vigibot/vigicad/images/Minus assembly/Final assembly-7.png

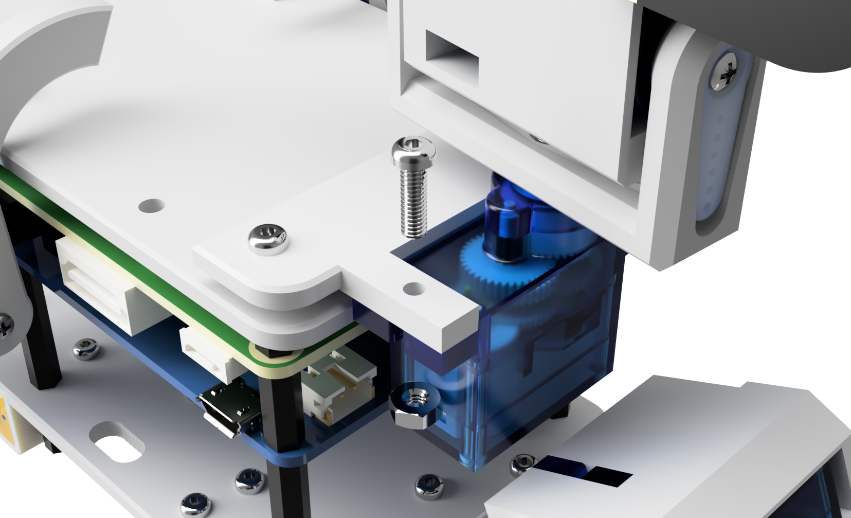
images/Minus assembly/Final assembly-7.png
