vigibot/vigicad/images/Minus render-1.png

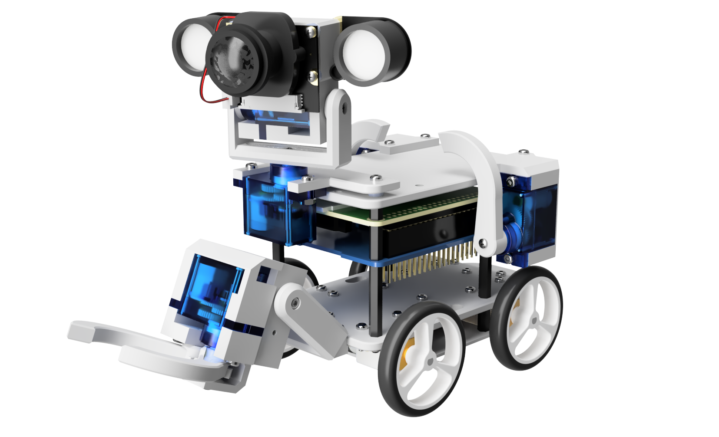
images/Minus render-1.png
