vigibot/vigicad/images/Minus render-2.png

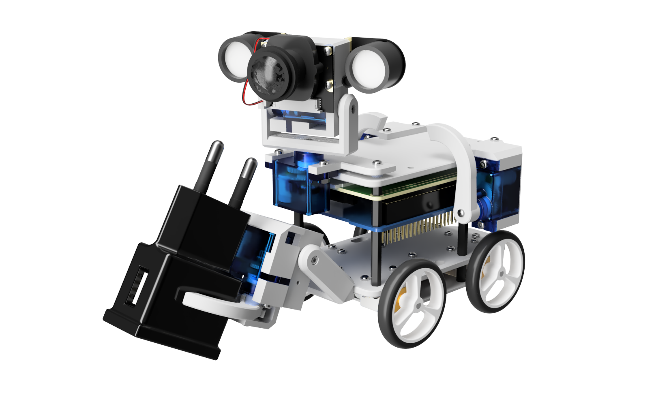
images/Minus render-2.png
