vigibot/vigicad/Minus 2S/Images/Minus 2s.jpg

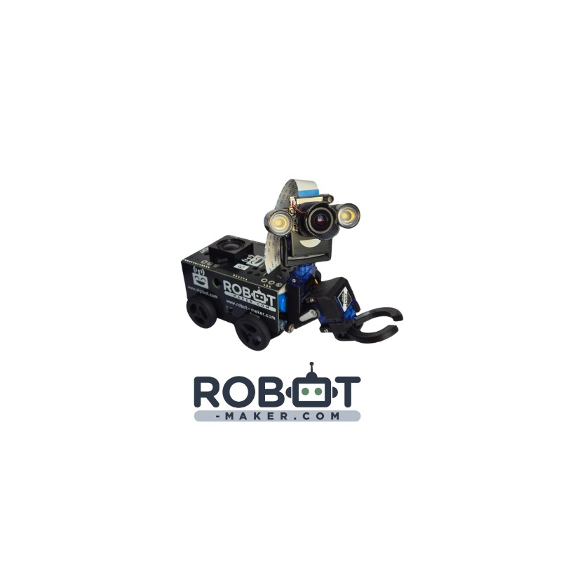
Minus 2S/Images/Minus 2s.jpg
