vigibot/vigicad/Minus 2S/3d Printed Parts/Body/Battery holder.step

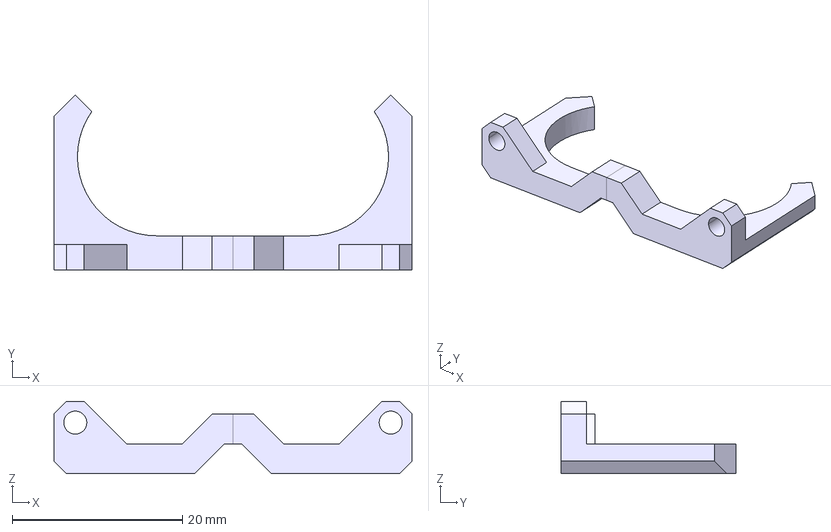
[picture p20: CAD file, 2026-06-20]
Minus 2S/3d Printed Parts/Body/Battery holder.step
42.0 x 20.5 x 8.50 mm
