vigibot/vigicad/Minus 2S/3d Printed Parts/Gripper/Gripper left finger.step

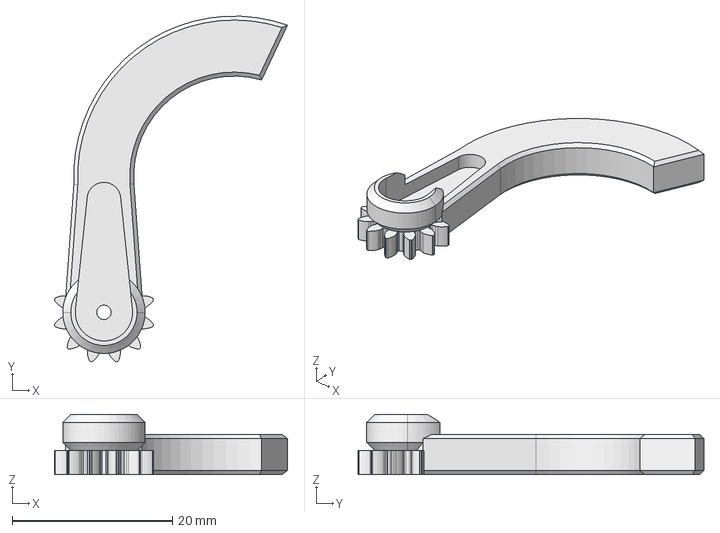
[picture p21: CAD file, 2026-06-20]
Minus 2S/3d Printed Parts/Gripper/Gripper left finger.step
29.1 x 43.1 x 7.50 mm
