vigibot/vigicad/Minus 2S/Pcb Boards/Head Led Pcb.step

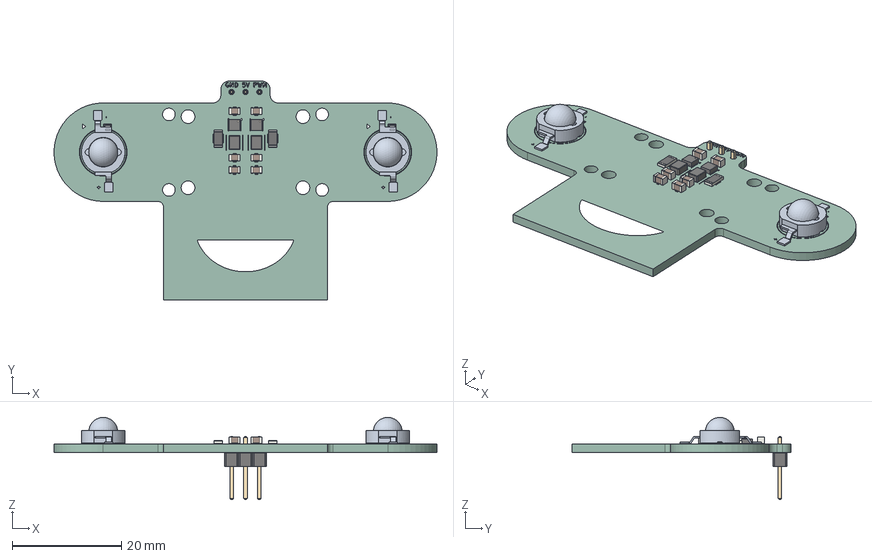
[picture p22: CAD file, 2026-06-20]
Minus 2S/Pcb Boards/Head Led Pcb.step
70.0 x 40.0 x 15.0 mm
C_0805_2012Metric x 6
L_Changjiang_FTC252012S x 2
R_1206_3216Metric x 2
Power Led x 2
WSON-6-1EP_2x2mm_P0.65mm_EP1x1.6mm x 2
PinHeader_1x03_P2.54mm_Vertical
Addon_head_silkscreen x 2
Addon_head_PCB
