vigibot/vigicad/3mf/rear_protection_long.3mf

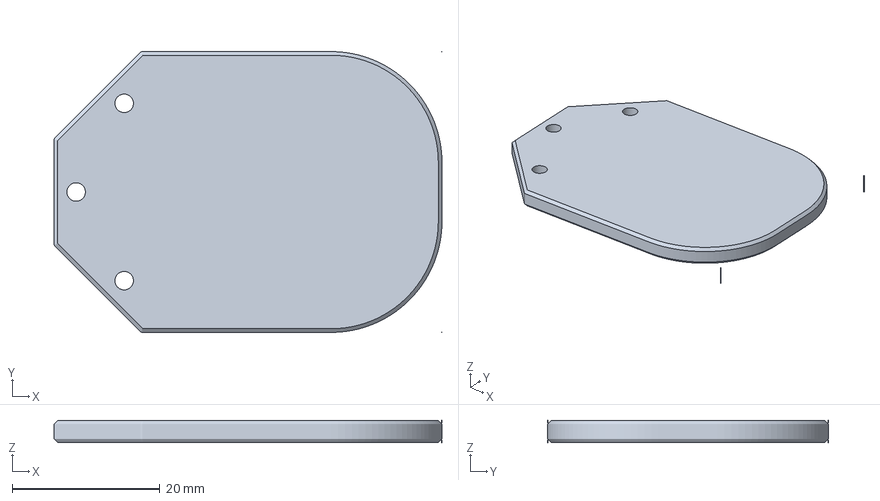
[picture p23: CAD file, 2019-10-13]
3mf/rear_protection_long.3mf
52.5 x 38.0 x 3.00 mm
