vigibot/vigicad/3mf/plate_middle_big_wheels.3mf

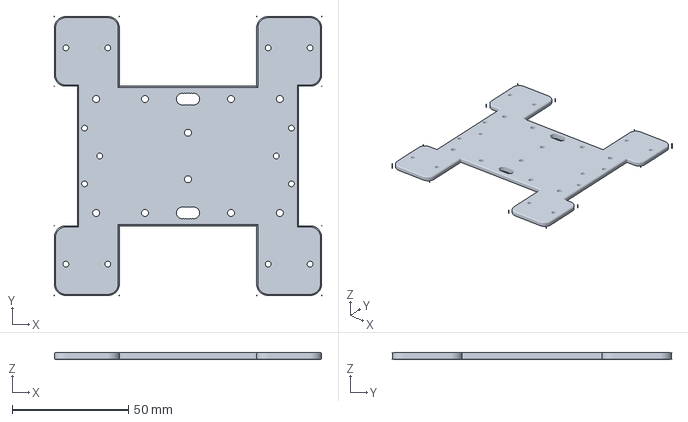
[picture p24: CAD file, 2019-10-09]
3mf/plate_middle_big_wheels.3mf
115.0 x 120.0 x 3.00 mm
