vigibot/vigicad/stl/UDroit35mm.stl

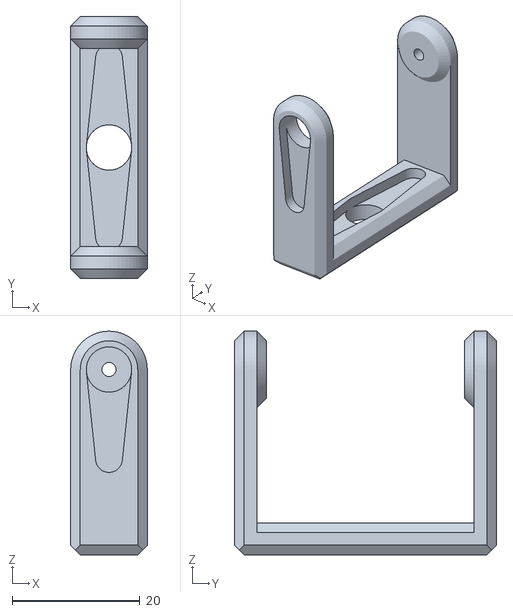
[picture p25: CAD file, 2019-06-25]
stl/UDroit35mm.stl
12.0 x 41.0 x 35.0
