vigibot/vigicad/3mf/head_pan_servo_bracket.3mf

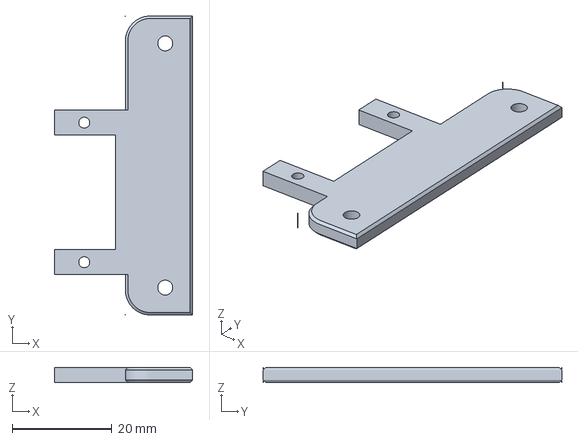
[picture p26: CAD file, 2019-09-12]
3mf/head_pan_servo_bracket.3mf
27.8 x 60.0 x 3.00 mm
