vigibot/vigicad/stl/UDroit30mm.stl

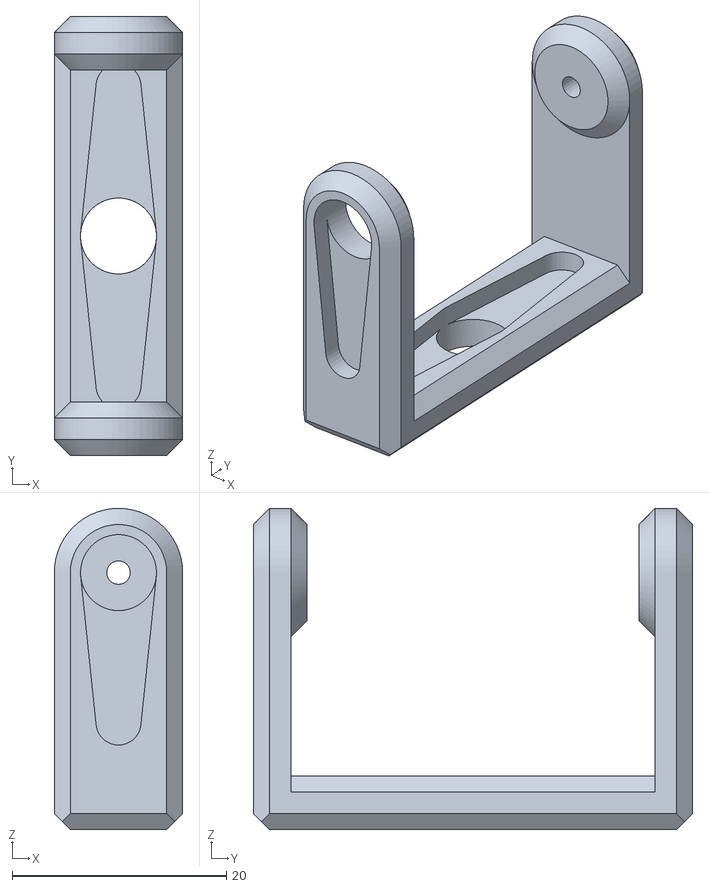
[picture p27: CAD file, 2019-06-25]
stl/UDroit30mm.stl
12.0 x 41.0 x 30.0
