vigibot/vigicad/3mf/generic_servo_bracket.3mf

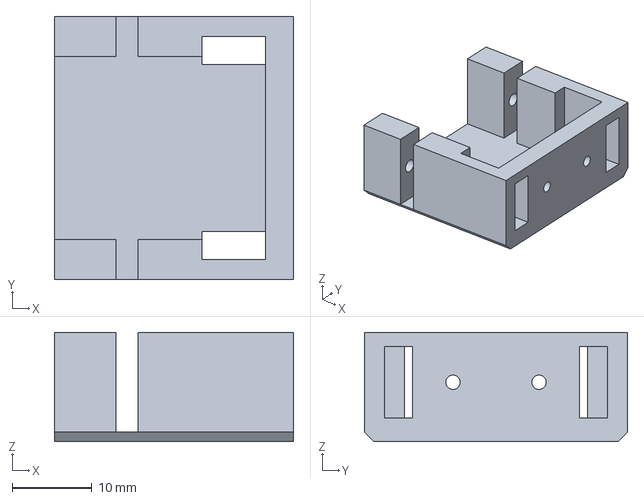
[picture p28: CAD file, 2019-09-08]
3mf/generic_servo_bracket.3mf
30.0 x 33.0 x 13.7 mm
