vigibot/vigicad/stl/UDroit28mm.stl

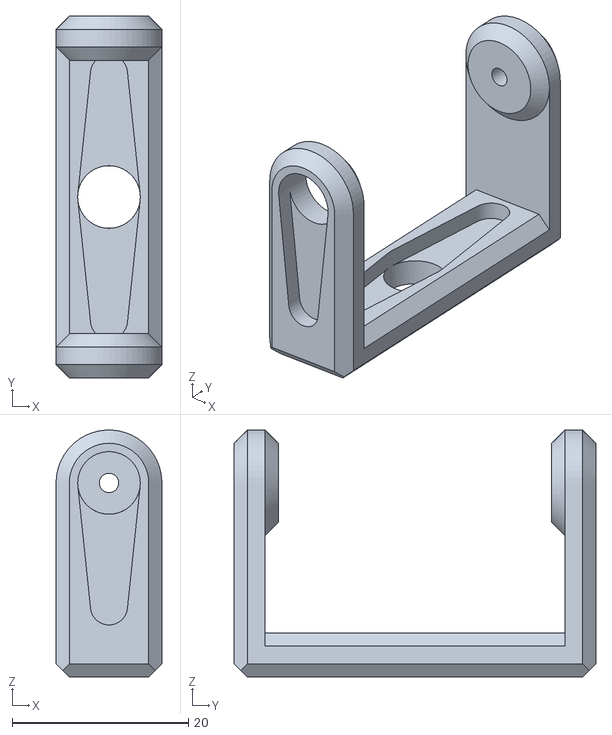
[picture p29: CAD file, 2019-06-25]
stl/UDroit28mm.stl
12.0 x 41.0 x 28.0
