vigibot/vigicad/3mf/usb_bracket.3mf

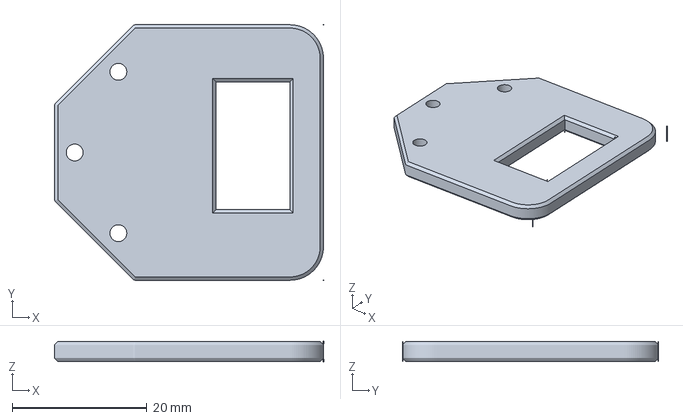
[picture p30: CAD file, 2019-09-07]
3mf/usb_bracket.3mf
40.0 x 38.0 x 3.00 mm
