vigibot/vigicad/3mf/get_up_servo_bracket_b.3mf

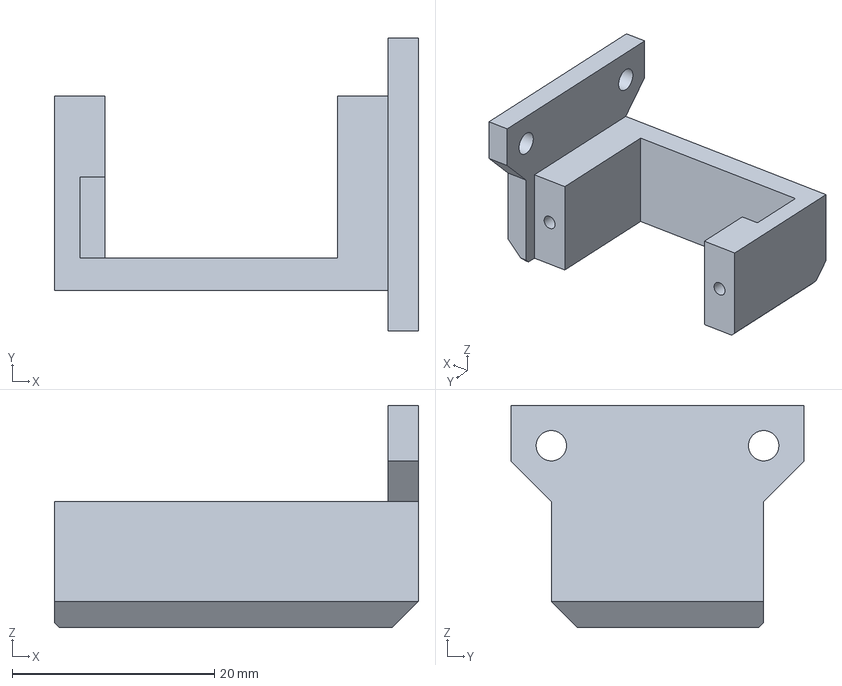
[picture p32: CAD file, 2019-09-06]
3mf/get_up_servo_bracket_b.3mf
36.0 x 29.0 x 22.0 mm
