vigibot/vigicad/3mf/rear_protection.3mf

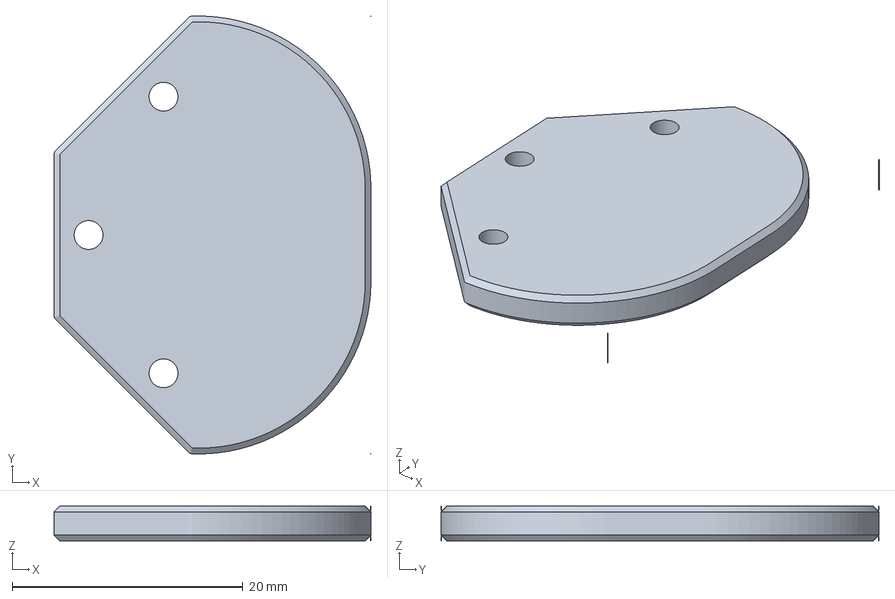
[picture p33: CAD file, 2019-09-06]
3mf/rear_protection.3mf
27.5 x 38.0 x 3.00 mm
