vigibot/vigicad/3mf/clamp_finger_b.3mf

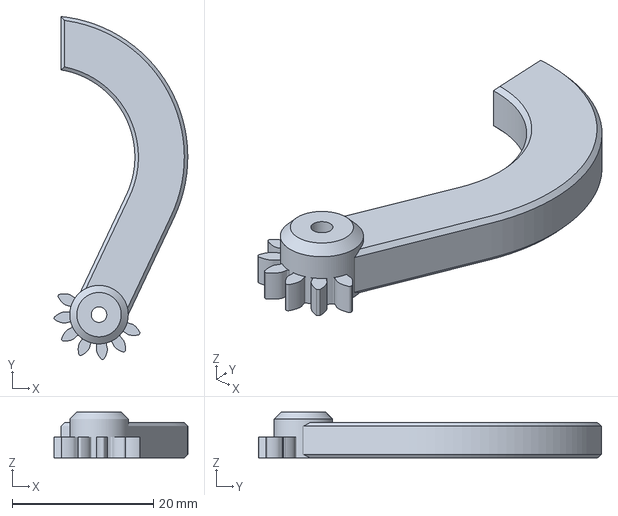
[picture p34: CAD file, 2019-09-06]
3mf/clamp_finger_b.3mf
18.9 x 48.6 x 6.50 mm
