vigibot/vigicad/3mf/plate_middle.3mf

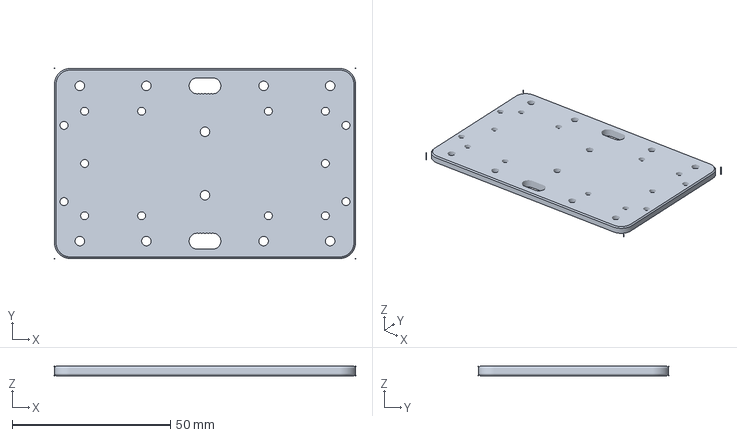
[picture p35: CAD file, 2019-09-06]
3mf/plate_middle.3mf
95.0 x 60.0 x 3.00 mm
