vigibot/vigicad/3mf/servo_finger_a.3mf

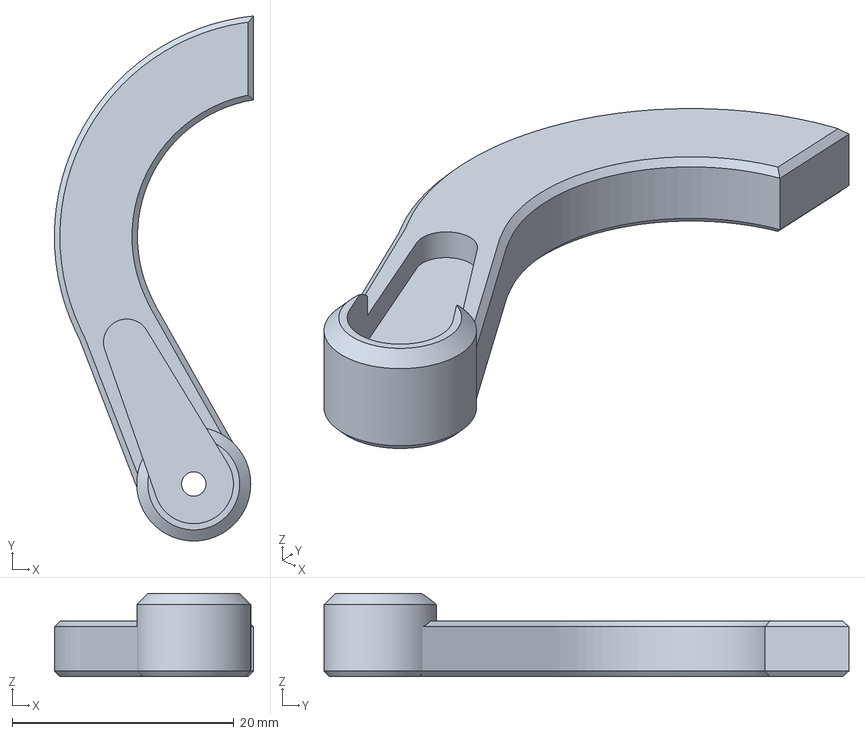
[picture p36: CAD file, 2019-09-06]
3mf/servo_finger_a.3mf
18.0 x 47.3 x 7.50 mm
