vigibot/vigicad/3mf/clamp_u_bracket.3mf

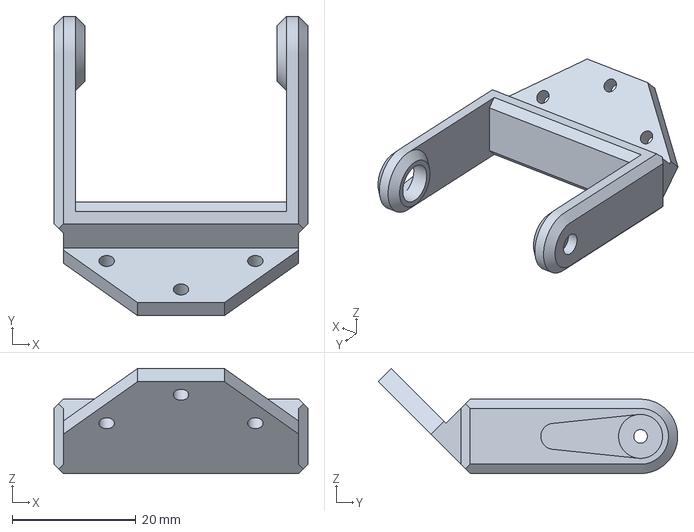
[picture p37: CAD file, 2019-09-06]
3mf/clamp_u_bracket.3mf
41.0 x 48.3 x 17.0 mm
