vigibot/vigicad/3mf/clamp_finger_a.3mf

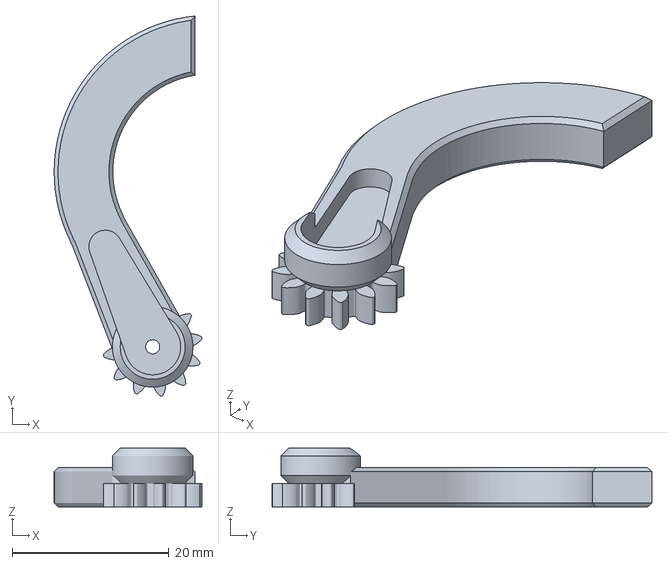
[picture p38: CAD file, 2019-09-06]
3mf/clamp_finger_a.3mf
18.9 x 48.5 x 7.50 mm
