vigibot/vigicad/3mf/plate_top_fan.3mf

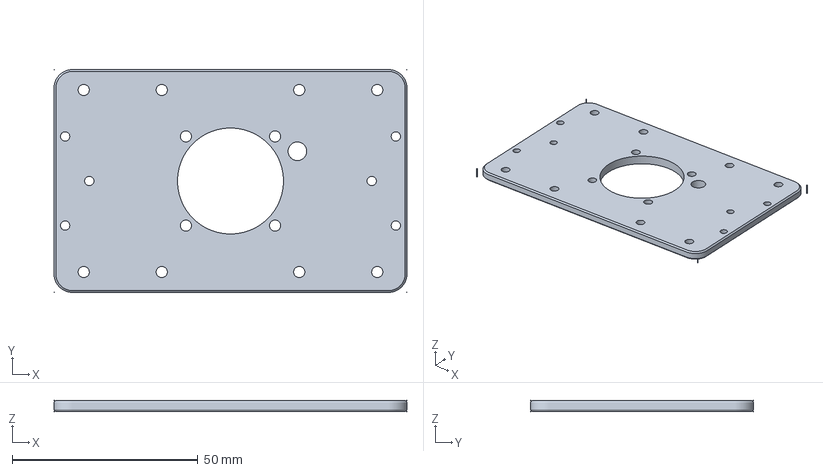
[picture p39: CAD file, 2019-09-06]
3mf/plate_top_fan.3mf
95.0 x 60.0 x 3.00 mm
