vigibot/vigicad/3mf/head_servo_camera_bracket_smile.3mf

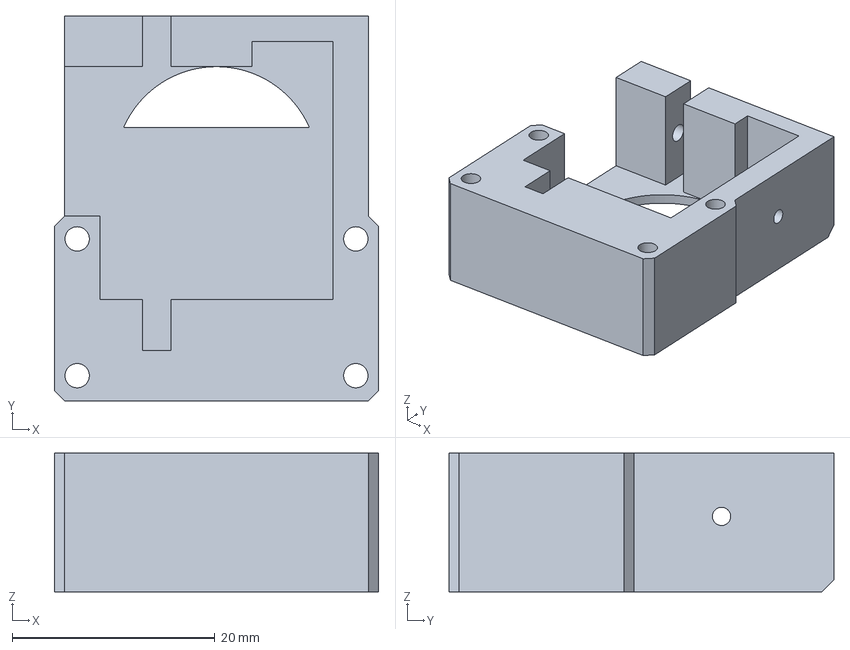
[picture p40: CAD file, 2019-09-06]
3mf/head_servo_camera_bracket_smile.3mf
32.0 x 38.0 x 13.7 mm
