vigibot/vigicad/3mf/photoresistor_cap.3mf

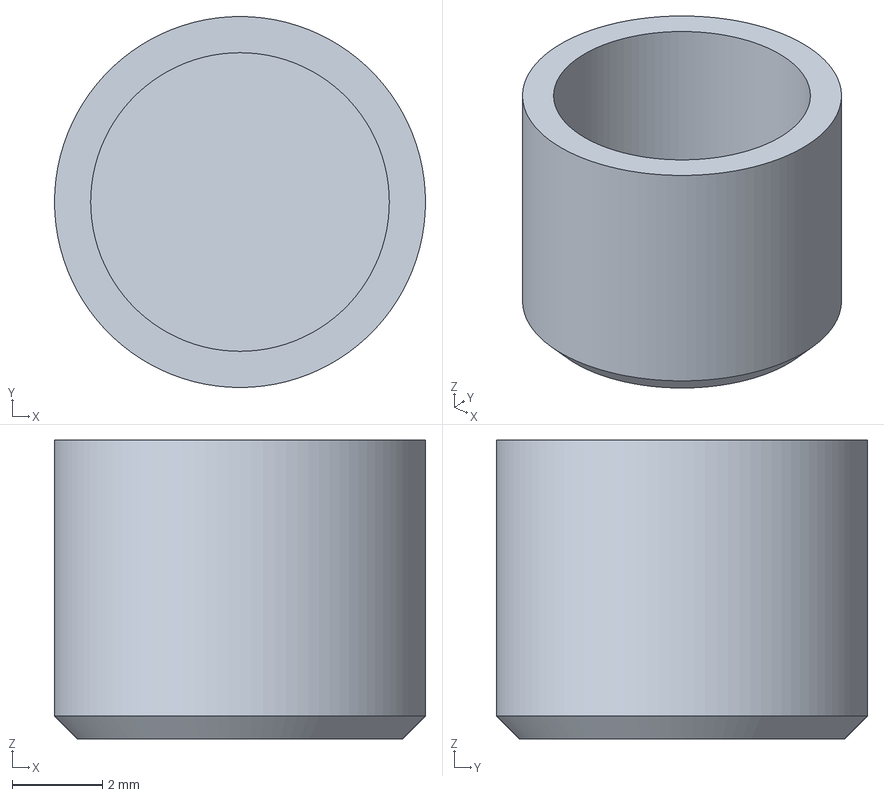
[picture p41: CAD file, 2019-09-06]
3mf/photoresistor_cap.3mf
8.20 x 8.20 x 6.60 mm
