vigibot/vigicad/3mf/plate_bottom.3mf

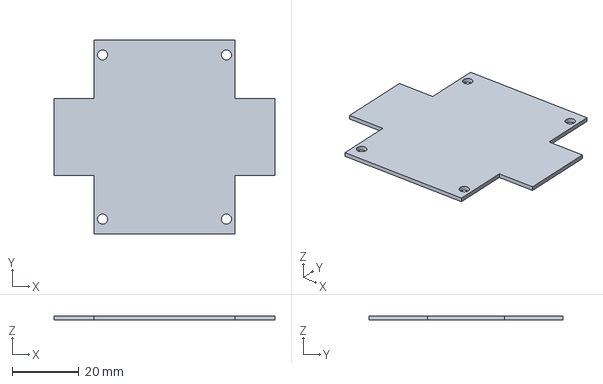
[picture p42: CAD file, 2019-09-06]
3mf/plate_bottom.3mf
66.0 x 58.0 x 1.20 mm
