vigibot/vigicad/images/Minus assembly/Camera assembly-1.png

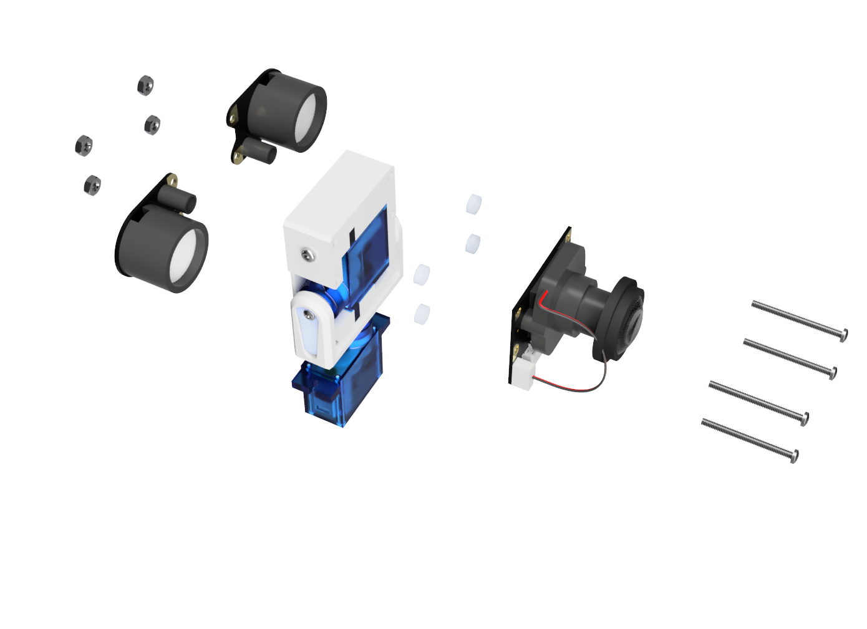
images/Minus assembly/Camera assembly-1.png
