vigibot/vigicad/images/Minus assembly/Camera assembly-2.png

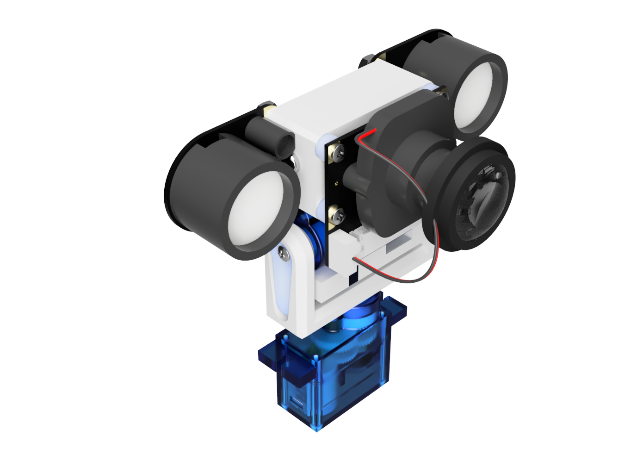
images/Minus assembly/Camera assembly-2.png
