vigibot/vigicad/images/Minus assembly/Final assembly-1.png

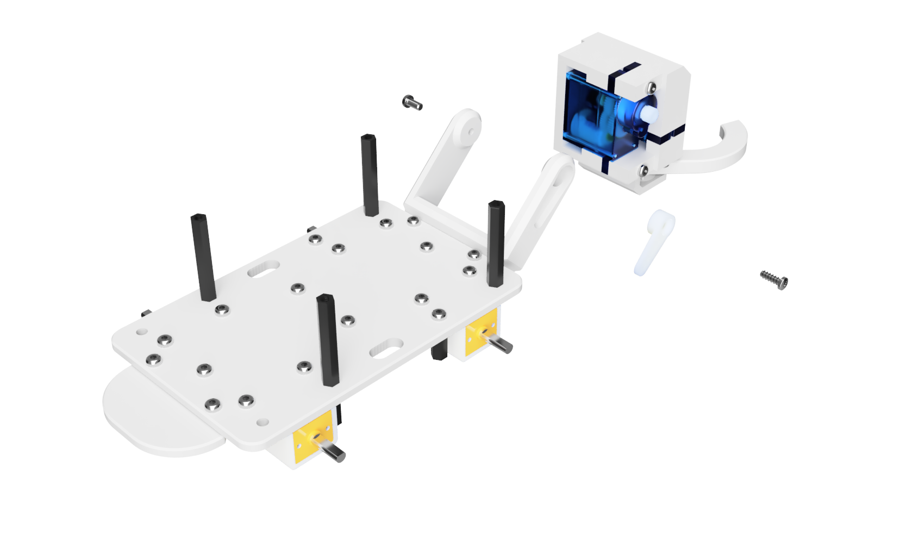
images/Minus assembly/Final assembly-1.png
