vigibot/vigicad/images/Minus assembly/Final assembly-3.png

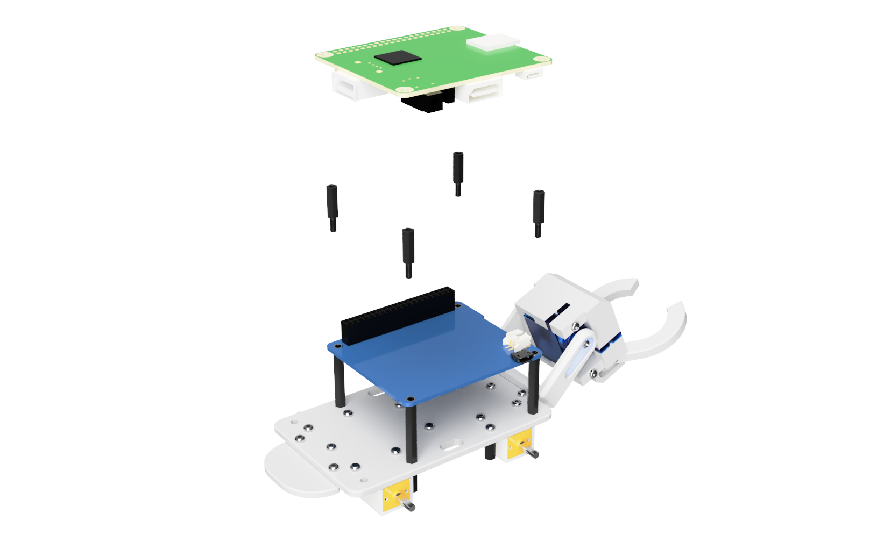
images/Minus assembly/Final assembly-3.png
