vigibot/vigicad/images/Minus assembly/Final assembly-4.png

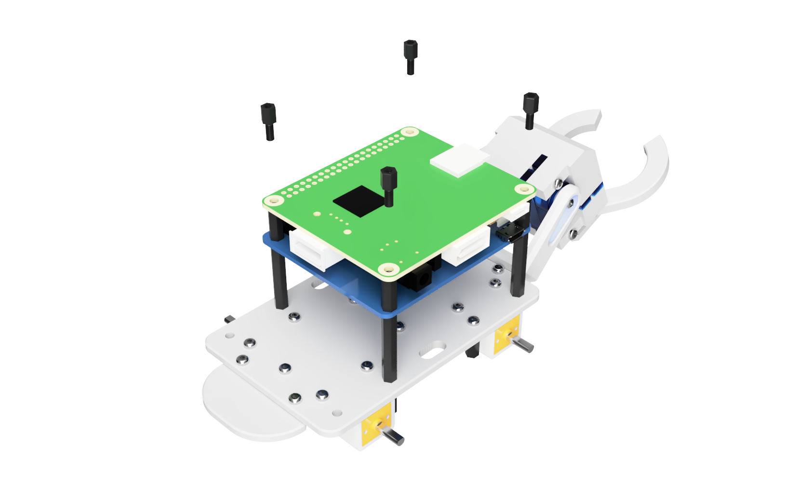
images/Minus assembly/Final assembly-4.png
