vigibot/vigicad/images/Minus assembly/Final assembly-5.png

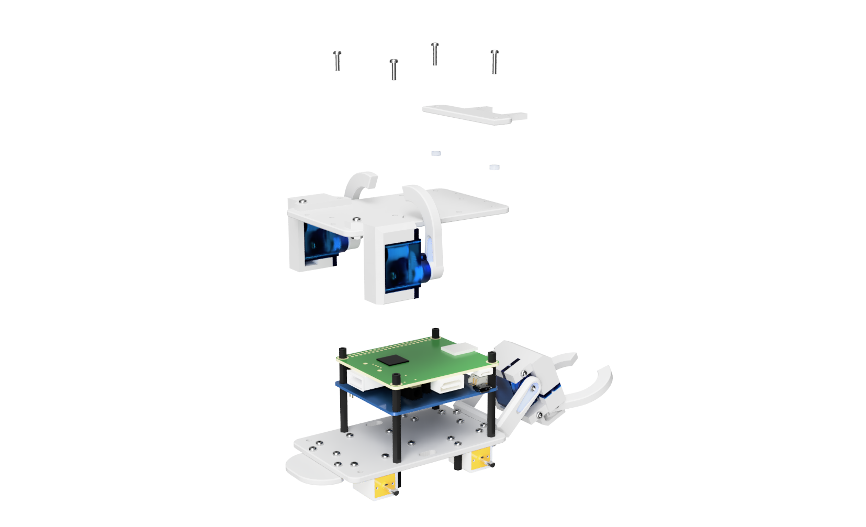
images/Minus assembly/Final assembly-5.png
