vigibot/vigicad/images/Minus assembly/Final assembly-6.png

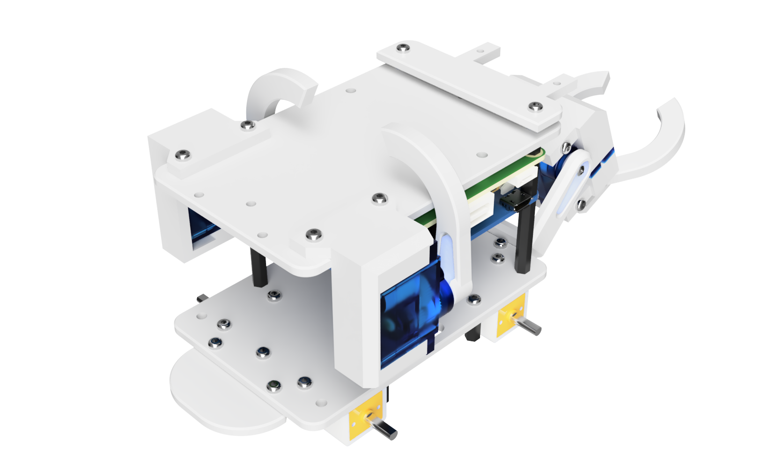
images/Minus assembly/Final assembly-6.png
