vigibot/vigicad/images/Minus assembly/Final assembly-9.png

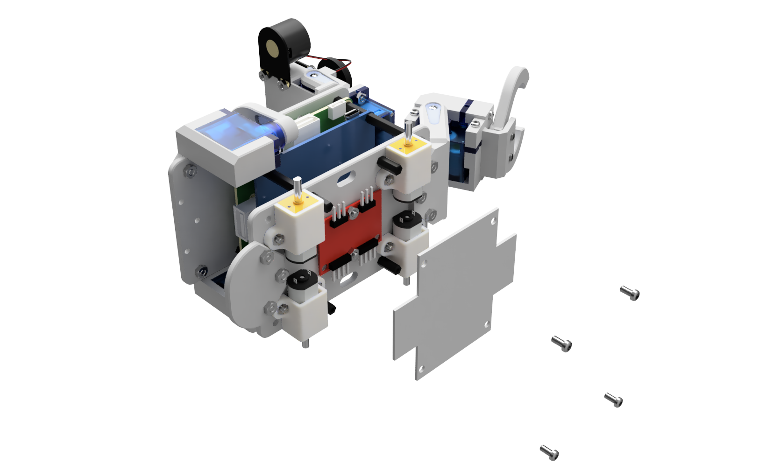
images/Minus assembly/Final assembly-9.png
