vigibot/vigicad/images/Minus assembly/Gripper assembly-1.png

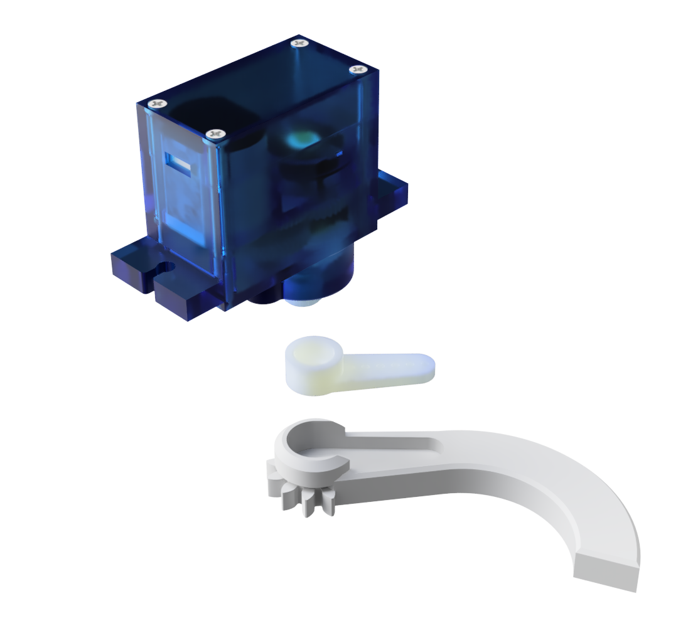
images/Minus assembly/Gripper assembly-1.png
