vigibot/vigicad/images/Minus assembly/Gripper assembly-2.png

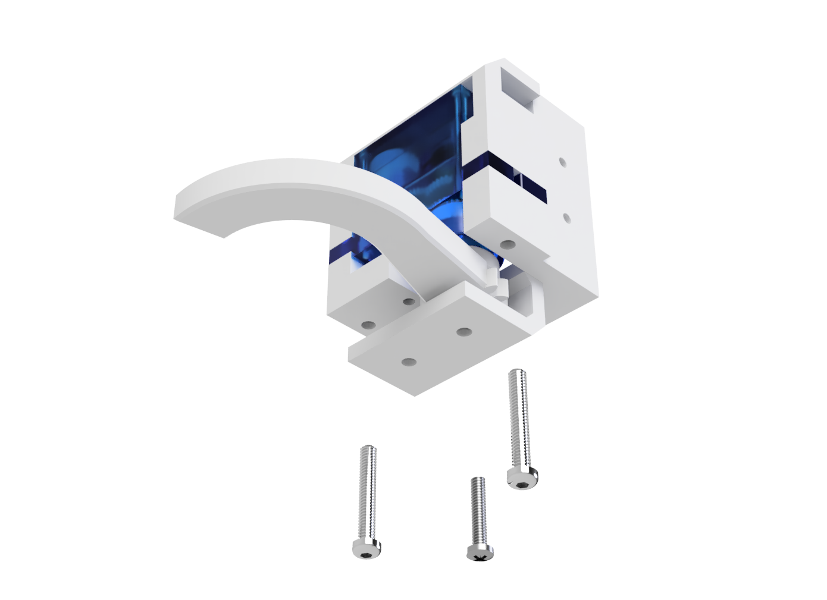
images/Minus assembly/Gripper assembly-2.png
