vigibot/vigicad/images/Minus assembly/Gripper assembly-3.png

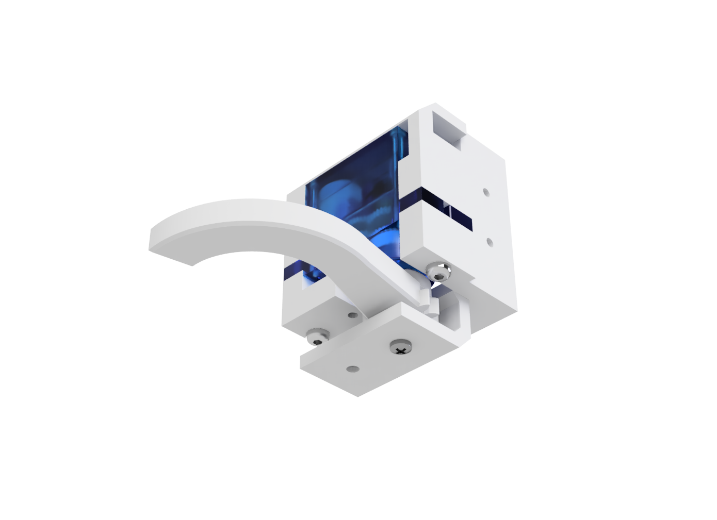
images/Minus assembly/Gripper assembly-3.png
