vigibot/vigicad/images/Minus assembly/Gripper assembly-4.png

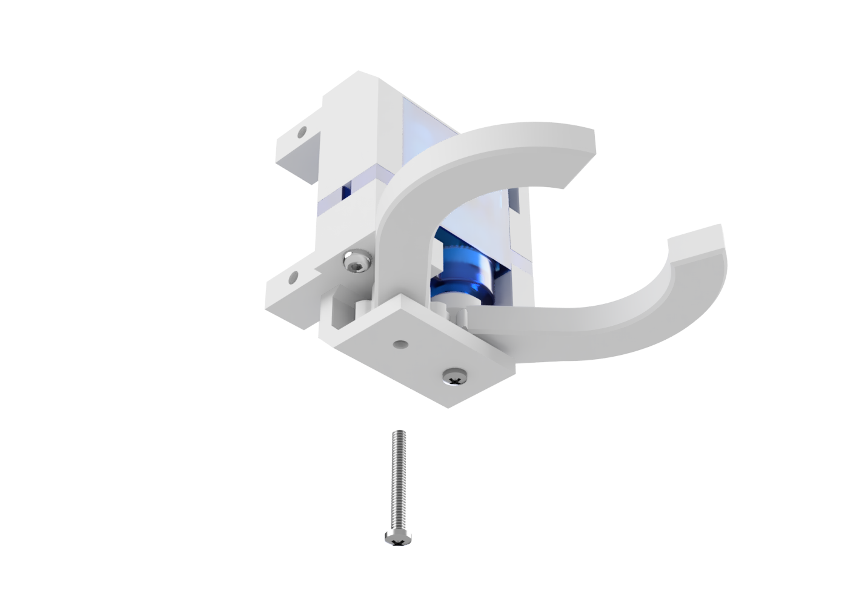
images/Minus assembly/Gripper assembly-4.png
