vigibot/vigicad/images/Minus assembly/Gripper assembly-6.png

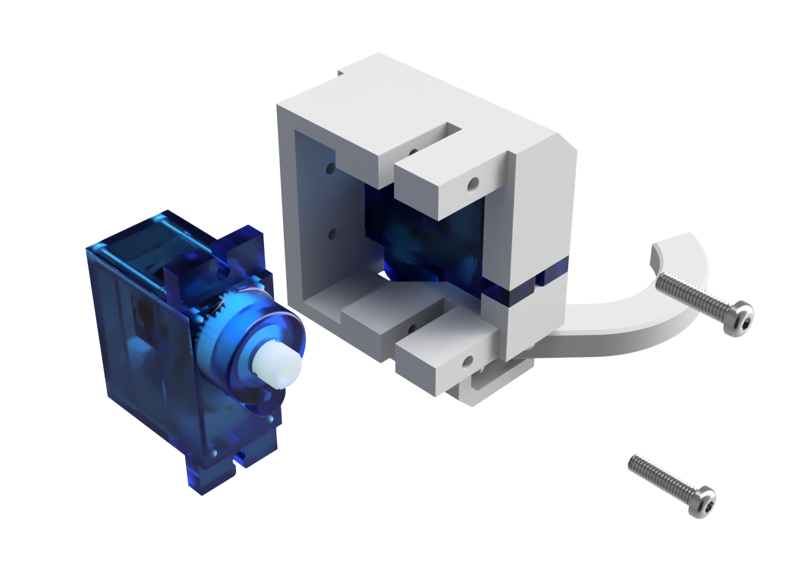
images/Minus assembly/Gripper assembly-6.png
