vigibot/vigicad/images/Minus assembly/Gripper assembly-7.png

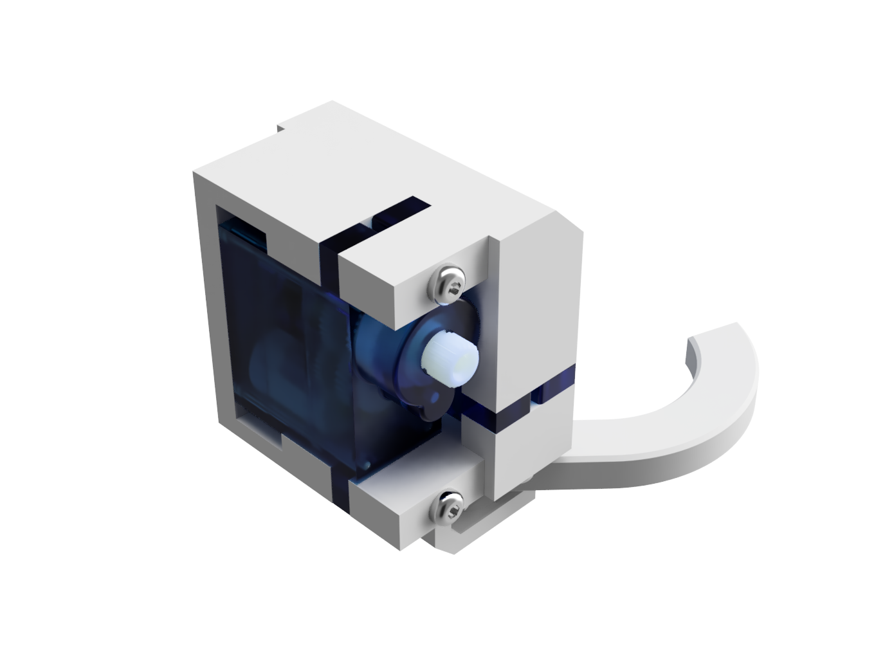
images/Minus assembly/Gripper assembly-7.png
