vigibot/vigicad/images/Minus assembly/Middle plate assembly-1.png

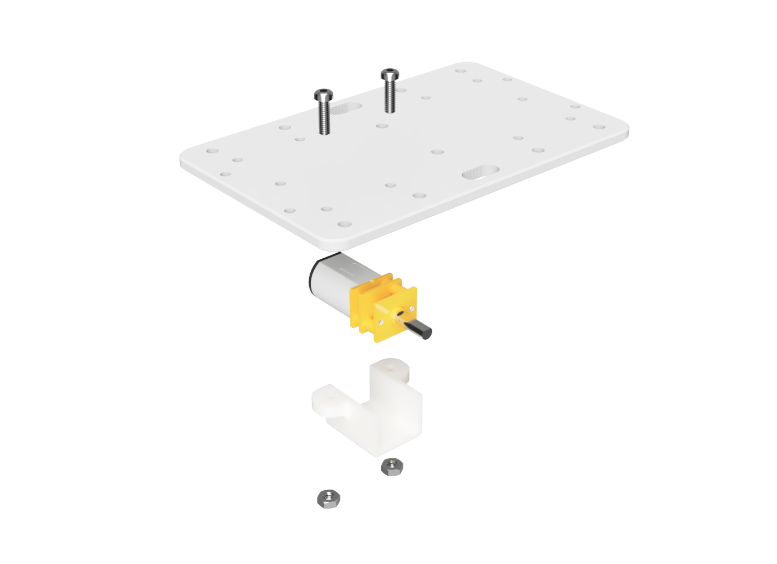
images/Minus assembly/Middle plate assembly-1.png
