vigibot/vigicad/images/Minus assembly/Middle plate assembly-2.png

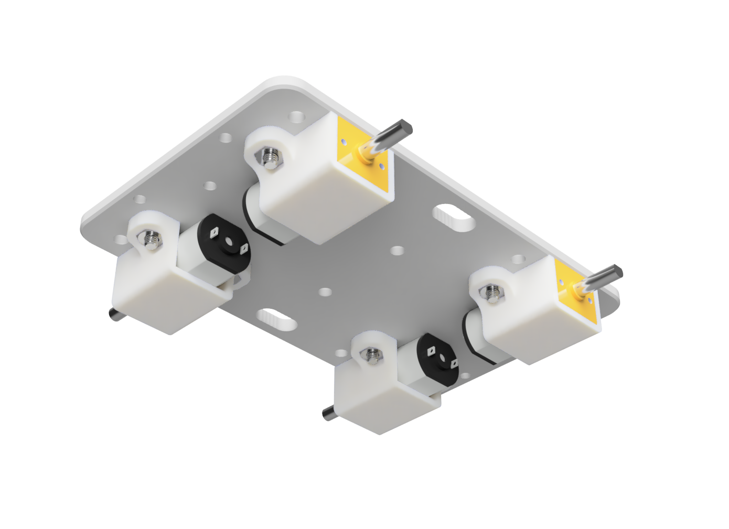
images/Minus assembly/Middle plate assembly-2.png
