vigibot/vigicad/images/Minus assembly/Middle plate assembly-3.png

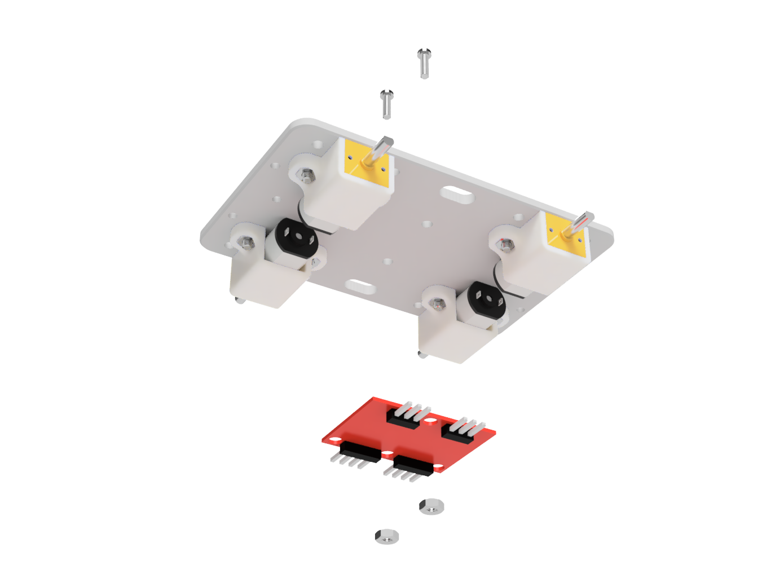
images/Minus assembly/Middle plate assembly-3.png
