vigibot/vigicad/images/Minus assembly/Middle plate assembly-4.png

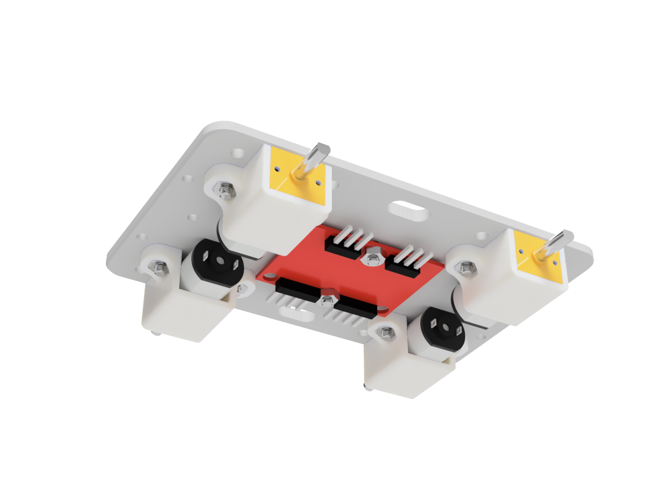
images/Minus assembly/Middle plate assembly-4.png
