vigibot/vigicad/images/Minus assembly/Middle plate assembly-5.png

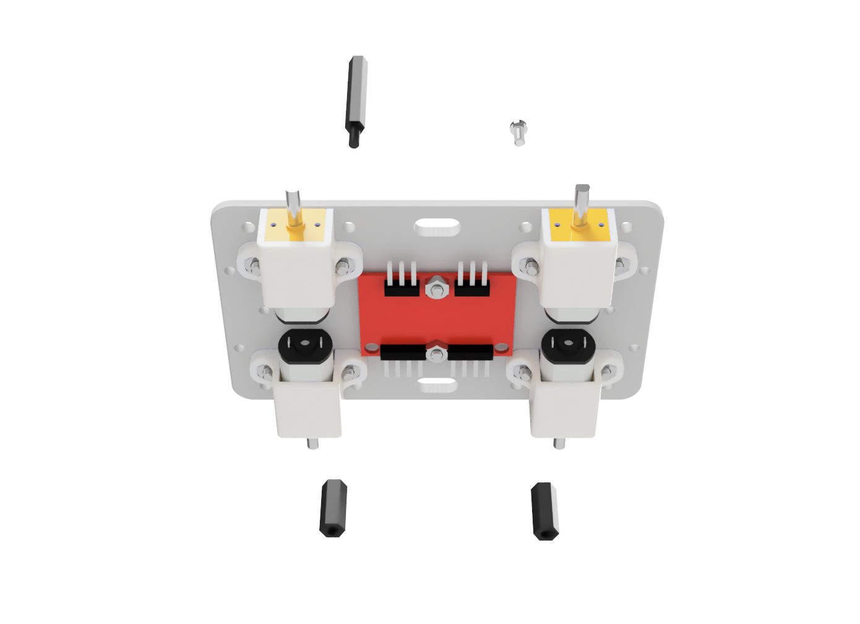
images/Minus assembly/Middle plate assembly-5.png
