vigibot/vigicad/images/Minus assembly/Middle plate assembly-6.png

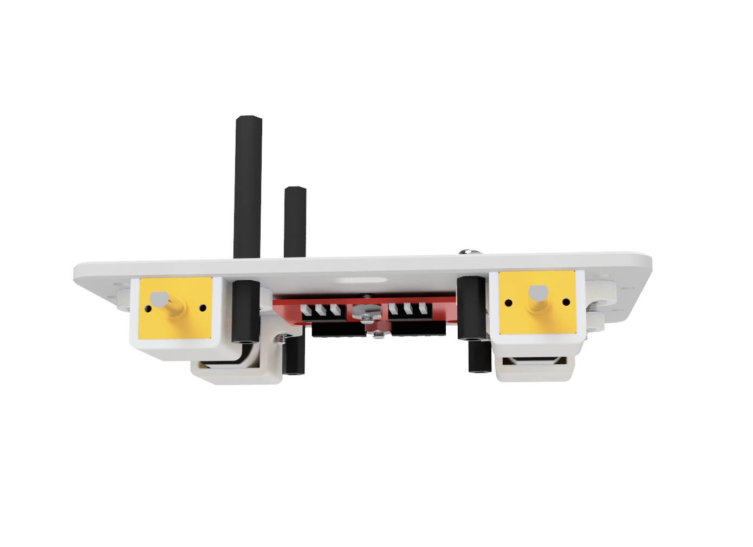
images/Minus assembly/Middle plate assembly-6.png
