vigibot/vigicad/images/Minus assembly/Middle plate assembly-8.png

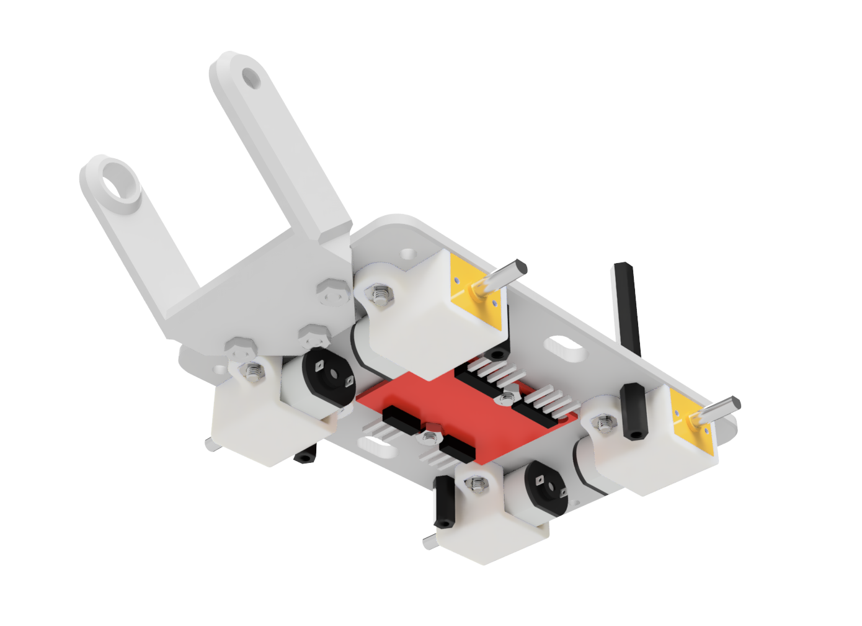
images/Minus assembly/Middle plate assembly-8.png
