vigibot/vigicad/images/Minus assembly/Middle plate assembly-9.png

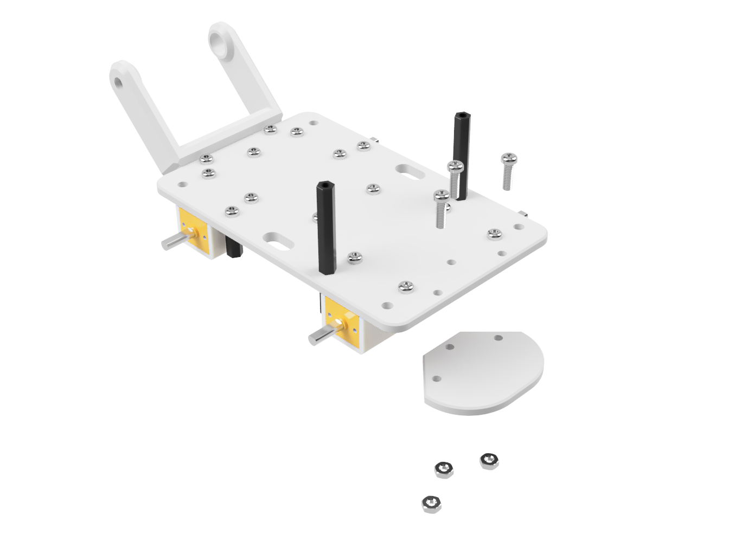
images/Minus assembly/Middle plate assembly-9.png
