vigibot/vigicad/images/Minus assembly/Middle plate assembly-10.png

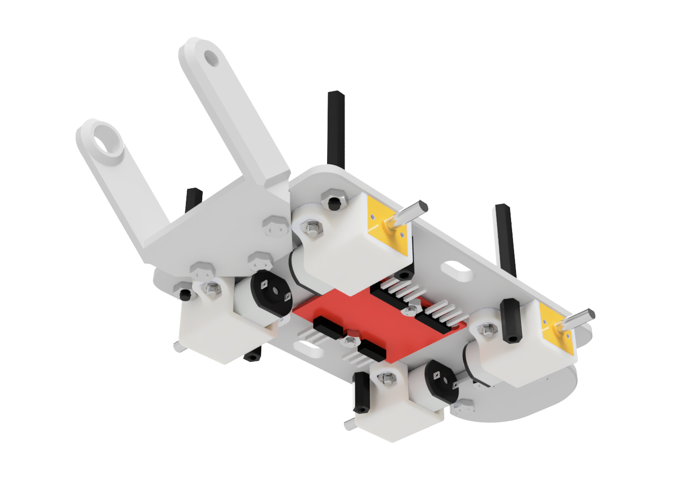
images/Minus assembly/Middle plate assembly-10.png
