vigibot/vigicad/images/Minus assembly/Pan + Tilt turret assembly-1.png

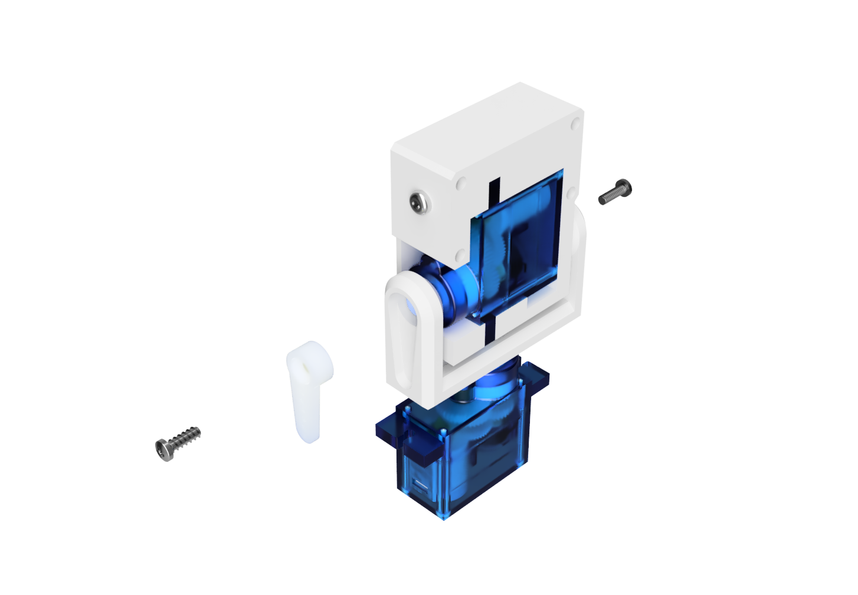
images/Minus assembly/Pan + Tilt turret assembly-1.png
