vigibot/vigicad/images/Minus assembly/Pan + Tilt turret assembly-2.png

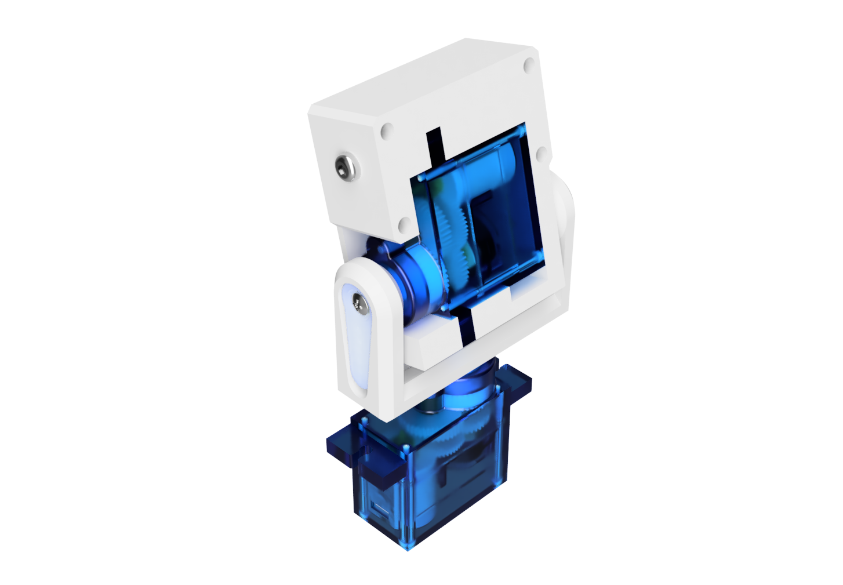
images/Minus assembly/Pan + Tilt turret assembly-2.png
