vigibot/vigicad/images/Minus assembly/Pan turret assembly-2.png

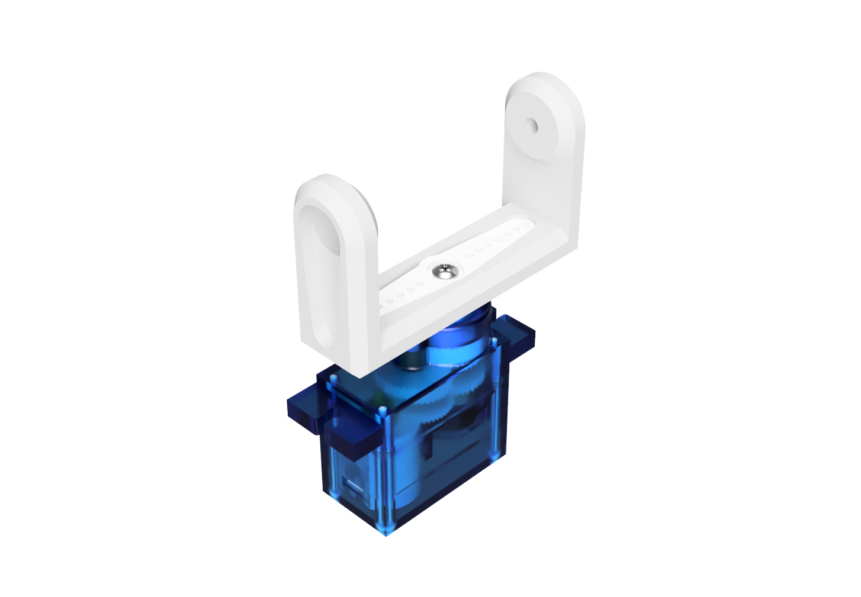
images/Minus assembly/Pan turret assembly-2.png
