vigibot/vigicad/images/Minus assembly/Side Arm A assembly-1.png

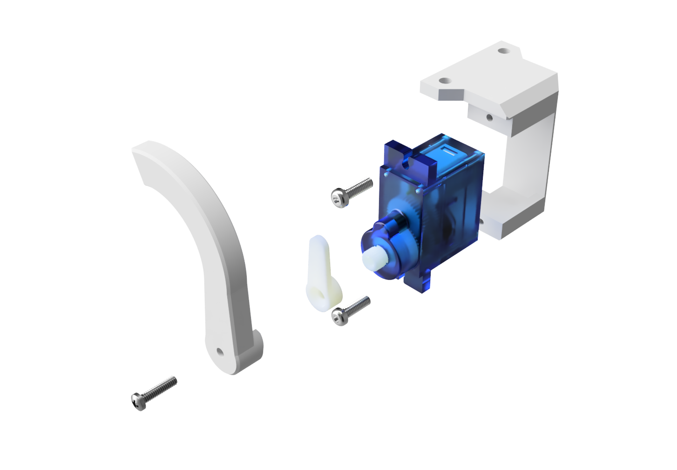
images/Minus assembly/Side Arm A assembly-1.png
