vigibot/vigicad/images/Minus assembly/Side Arm B assembly.png

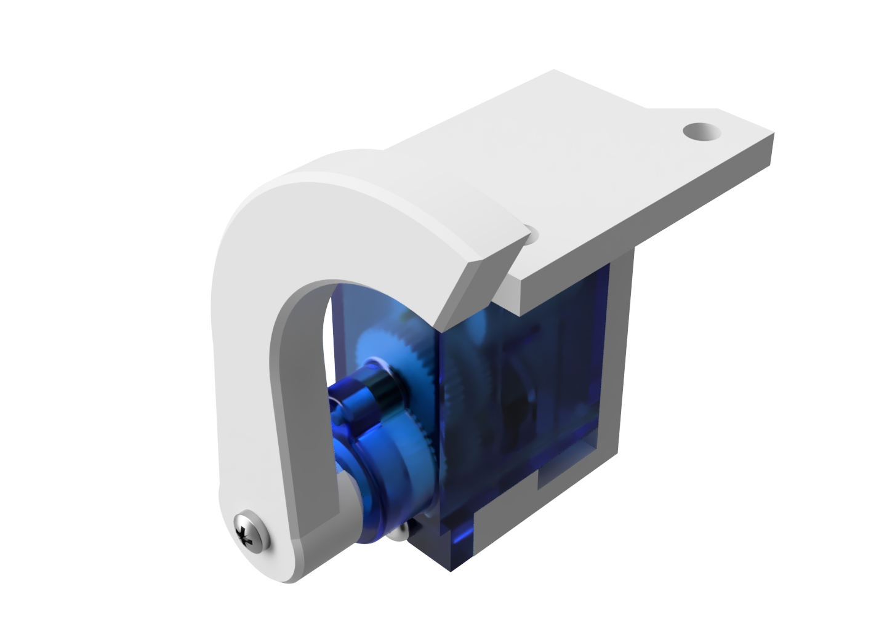
images/Minus assembly/Side Arm B assembly.png
