vigibot/vigicad/images/Minus assembly/Tilt turret assembly-1.png

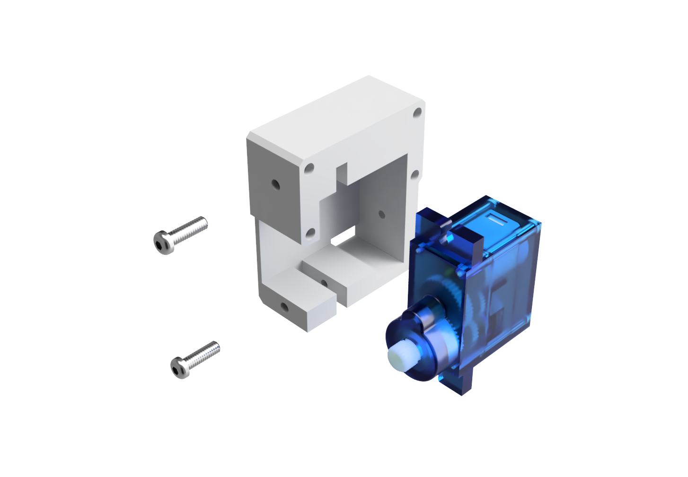
images/Minus assembly/Tilt turret assembly-1.png
