vigibot/vigicad/images/Minus assembly/Tilt turret assembly-2.png

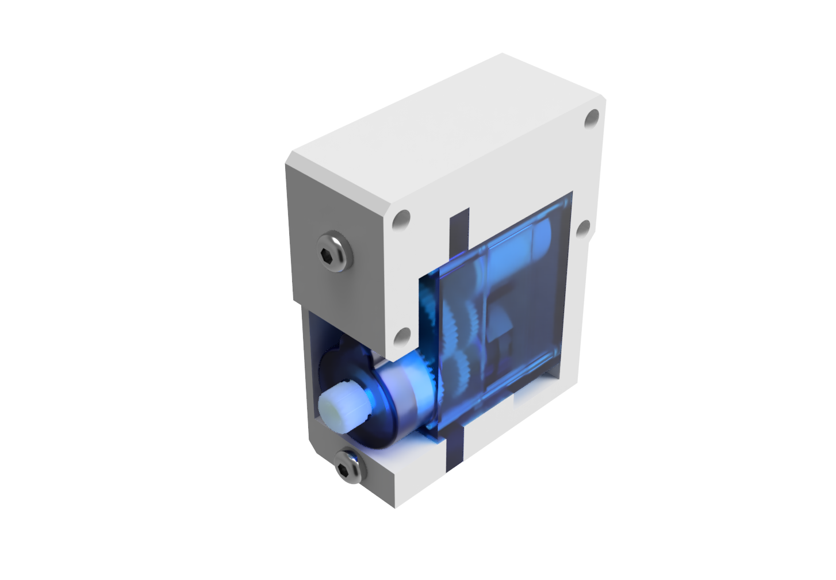
images/Minus assembly/Tilt turret assembly-2.png
