vigibot/vigicad/images/Minus assembly/Top plate assembly-1.png

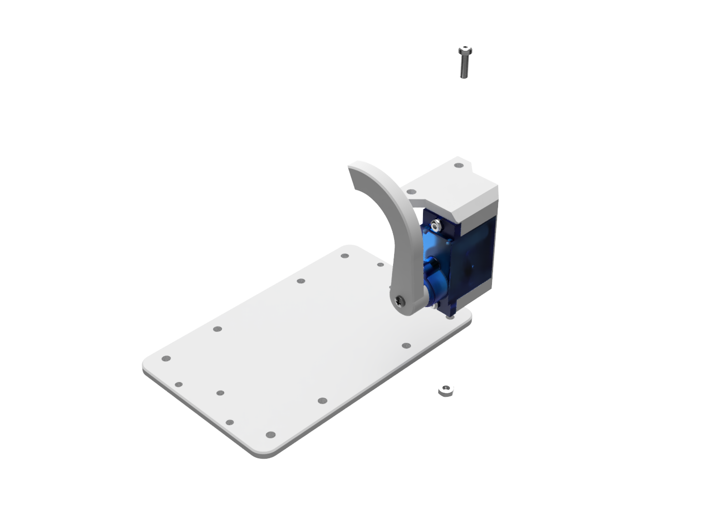
images/Minus assembly/Top plate assembly-1.png
