vigibot/vigicad/images/Minus assembly/Top plate assembly-2.png

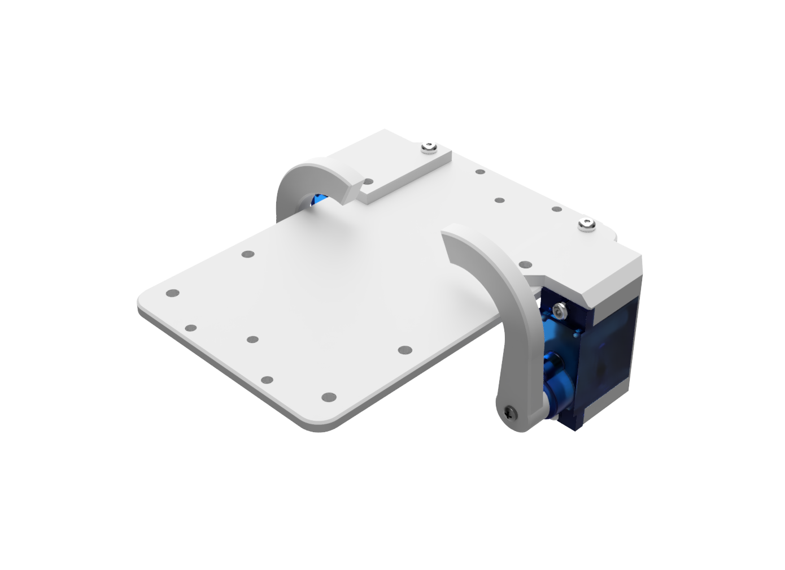
images/Minus assembly/Top plate assembly-2.png
